nemethakos/christmas_star/ChristmasStar.h

#ifndef CHRISTMASSTAR_H_
#define CHRISTMASSTAR_H_

#include <FastLED.h>
#include "BoardSettings.h"
#include <Arduino.h>
#include <HardwareSerial.h>

#include <lib8tion/math8.h>
#include <lib8tion.h>

#include <stdint.h>

#include "debug.h"

/**
 * Buffer for FastLED
 */
CRGB ledBuffer[NUMBER_OF_LEDS];

#endif /* CHRISTMASSTAR_H_ */
