nemethakos/christmas_star/BoardSettings.h

#ifndef BOARDSETTINGS_H_
#define BOARDSETTINGS_H_

/**
 * Number of APA102 LEDs in board
 */
#define NUMBER_OF_LEDS (31)

/**
 * APA102 is enabled by pulling PIN 4 LOW
 */
#define APA102_ENABLE_PIN 4

/**
 * APDS INT line is connected to PIN 2 - INTERRUPT 0
 */
#define APDS_INTERRUPT 0


#endif /* BOARDSETTINGS_H_ */
